jsenlas/STM32WB55_proj/pic/USB_cross.png

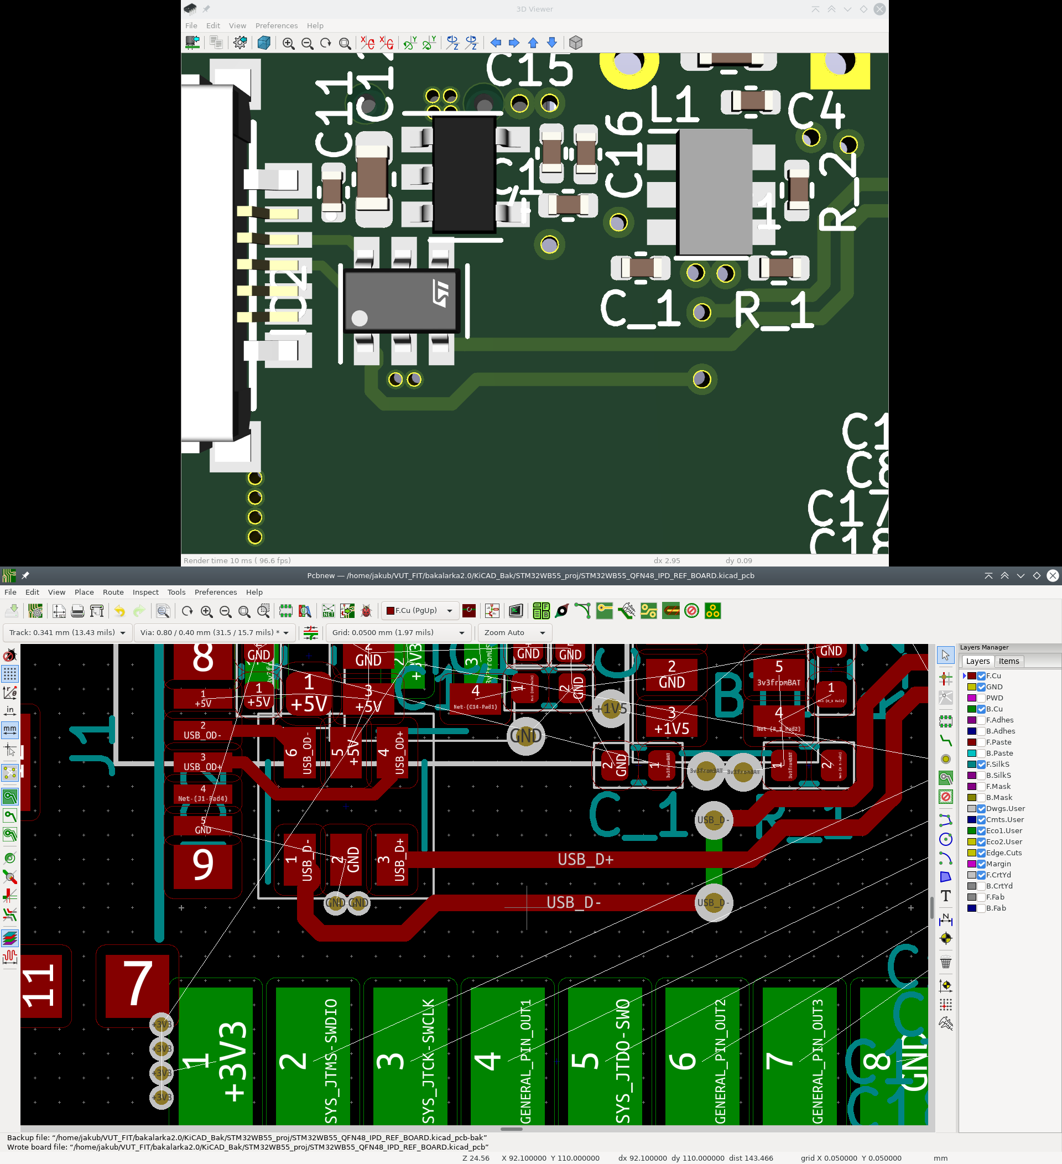
pic/USB_cross.png
